PostTenebrasLab/PTL-ino/hardware/pictures/PTLino_back.png

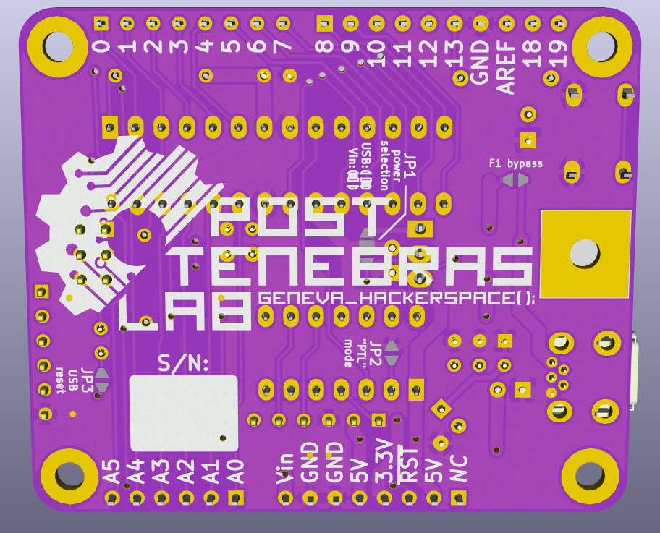
hardware/pictures/PTLino_back.png
