PostTenebrasLab/PTL-ino/hardware/pictures/PTLino_front.png

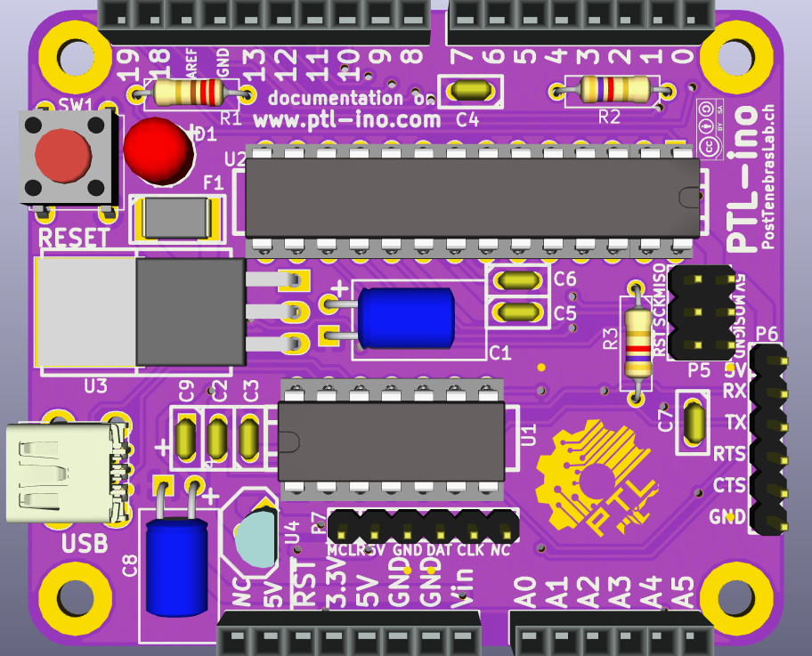
hardware/pictures/PTLino_front.png
