PostTenebrasLab/PTL-ino/shield_template/meta/brd.png

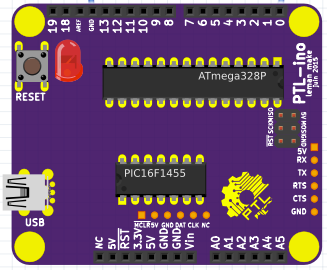
shield_template/meta/brd.png
