PostTenebrasLab/PTL-ino/doc/img/step5b.medium.jpg

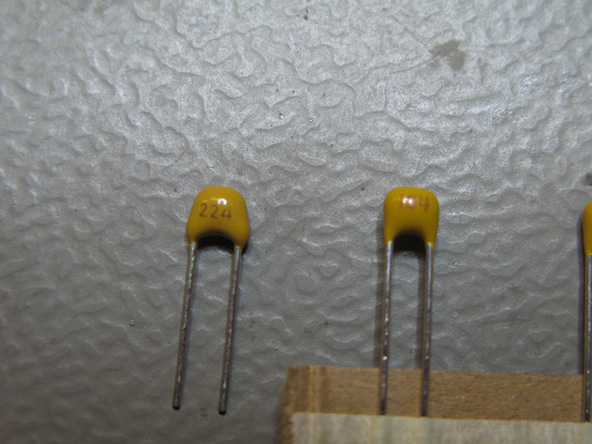
doc/img/step5b.medium.jpg
